MohamedAlDeep/EEG-Headset/Media/image-1.png

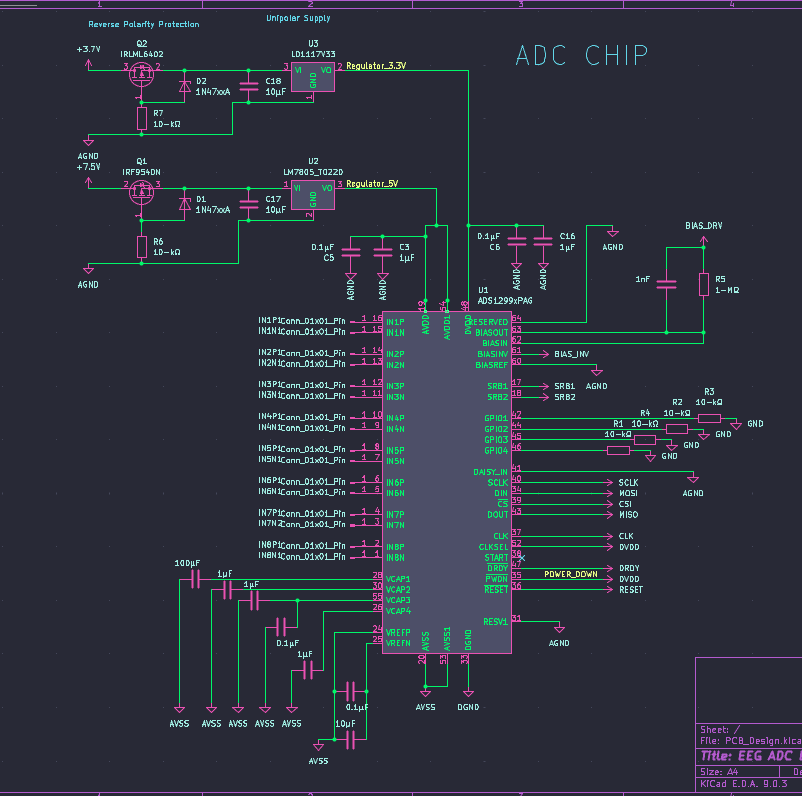
Media/image-1.png
